makersmakingchange/One-Handed_Xbox_One_Controller_Modification/Build_Files/3D_Printing_Files/Right-Handed Mod/XBONE right handed.stl

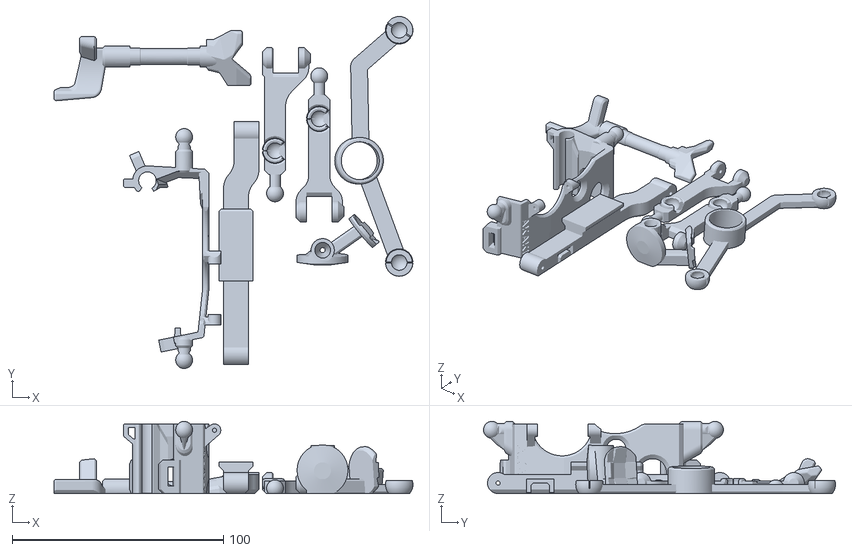
[picture p19: CAD file, 2023-02-23]
Build_Files/3D_Printing_Files/Right-Handed Mod/XBONE right handed.stl
169.9 x 166.7 x 34.2
