makersmakingchange/One-Handed_Xbox_One_Controller_Modification/Build_Files/3D_Printing_Files/Left-Handed Mod/LH-Y_Button_Extender.stl

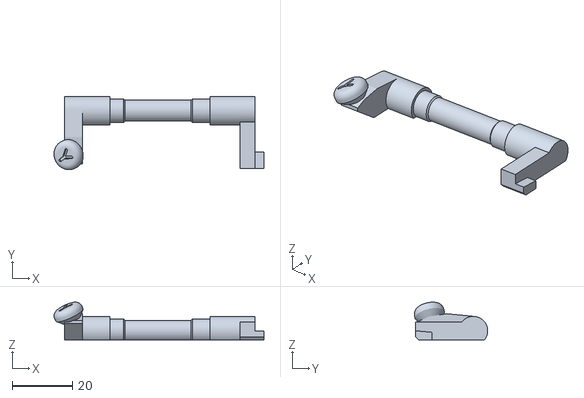
[picture p20: CAD file, 2023-03-06]
Build_Files/3D_Printing_Files/Left-Handed Mod/LH-Y_Button_Extender.stl
69.7 x 24.4 x 12.5
