makersmakingchange/One-Handed_Xbox_One_Controller_Modification/Build_Files/3D_Printing_Files/Left-Handed Mod/LH-Thumbstick_Arm.stl

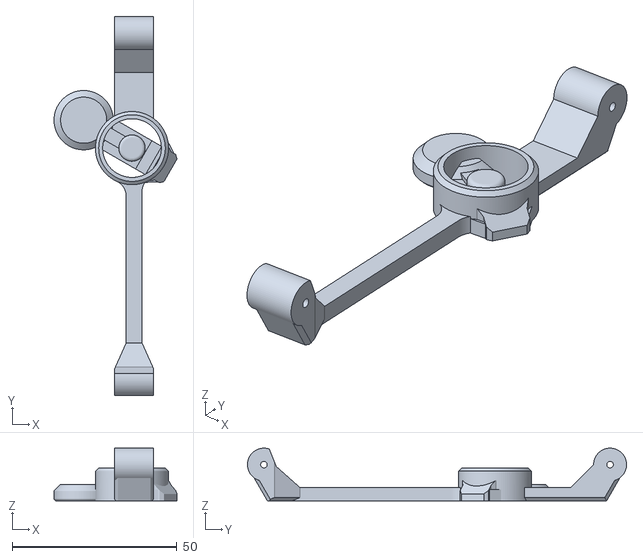
[picture p21: CAD file, 2023-03-06]
Build_Files/3D_Printing_Files/Left-Handed Mod/LH-Thumbstick_Arm.stl
37.3 x 115.0 x 16.0
