makersmakingchange/One-Handed_Xbox_One_Controller_Modification/Build_Files/3D_Printing_Files/Left-Handed Mod/LH-B_Button_Extender.stl

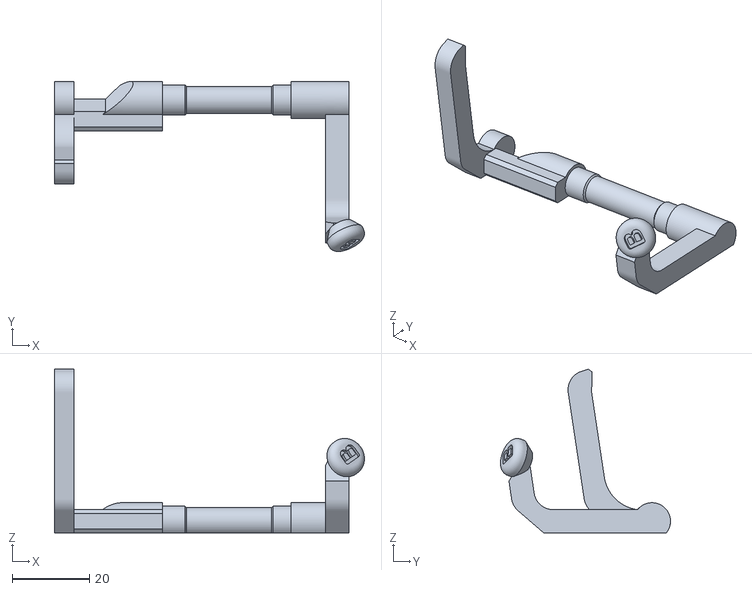
[picture p22: CAD file, 2023-03-06]
Build_Files/3D_Printing_Files/Left-Handed Mod/LH-B_Button_Extender.stl
80.2 x 44.0 x 42.4
