makersmakingchange/One-Handed_Xbox_One_Controller_Modification/Build_Files/3D_Printing_Files/Left-Handed Mod/XBONE left handed.stl

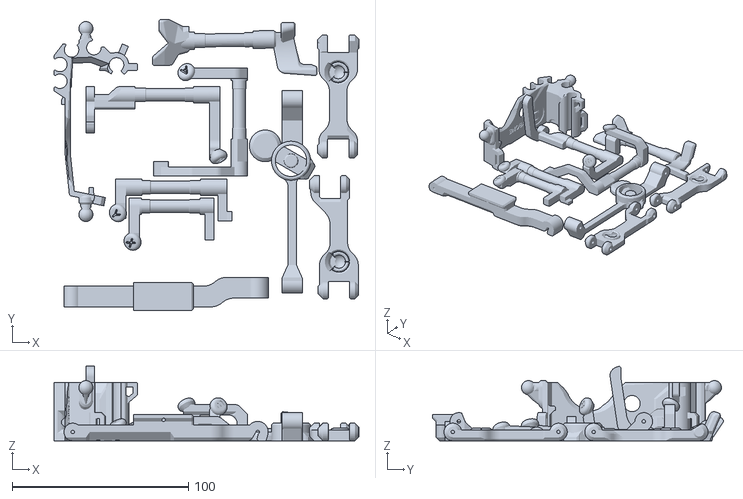
[picture p23: CAD file, 2023-02-23]
Build_Files/3D_Printing_Files/Left-Handed Mod/XBONE left handed.stl
173.2 x 165.4 x 42.4
